fachat/MicroPET/Board/micropet_v2-brd.png

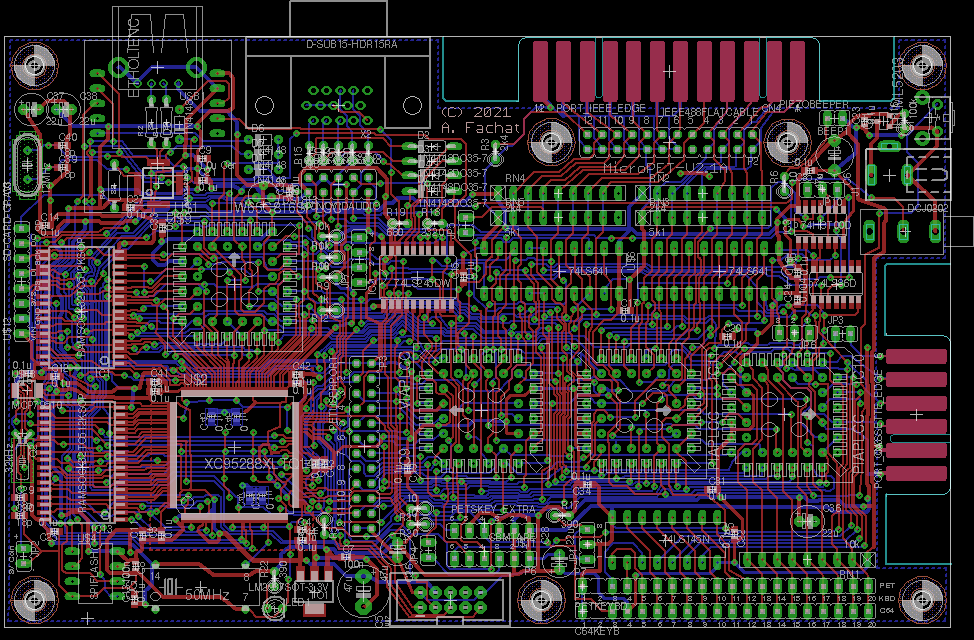
Board/micropet_v2-brd.png
