fachat/MicroPET/Board/micropet_v2-layout.png

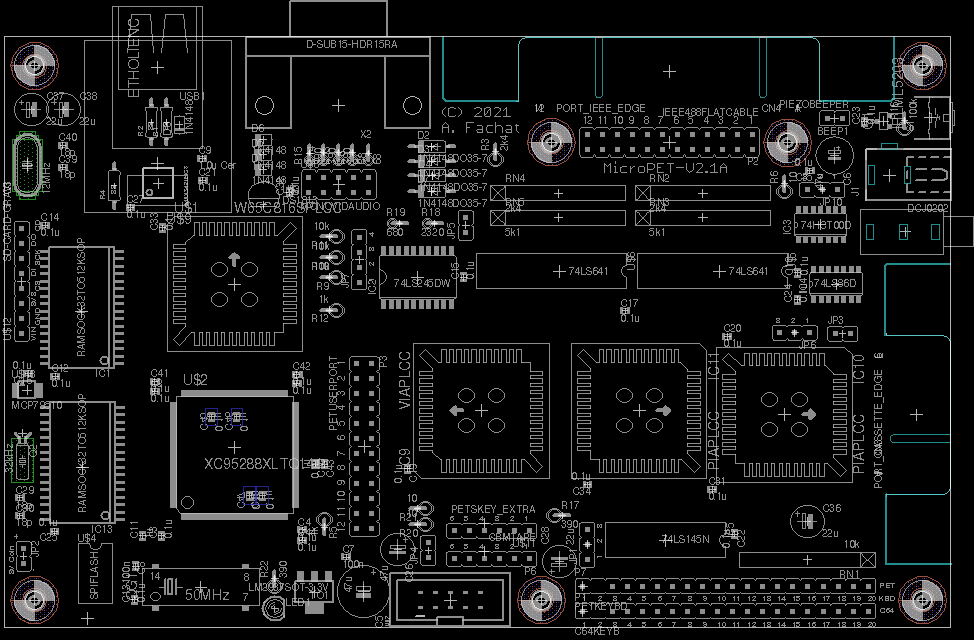
Board/micropet_v2-layout.png
