fachat/MicroPET/Board/micropet_v2-sch-1.png

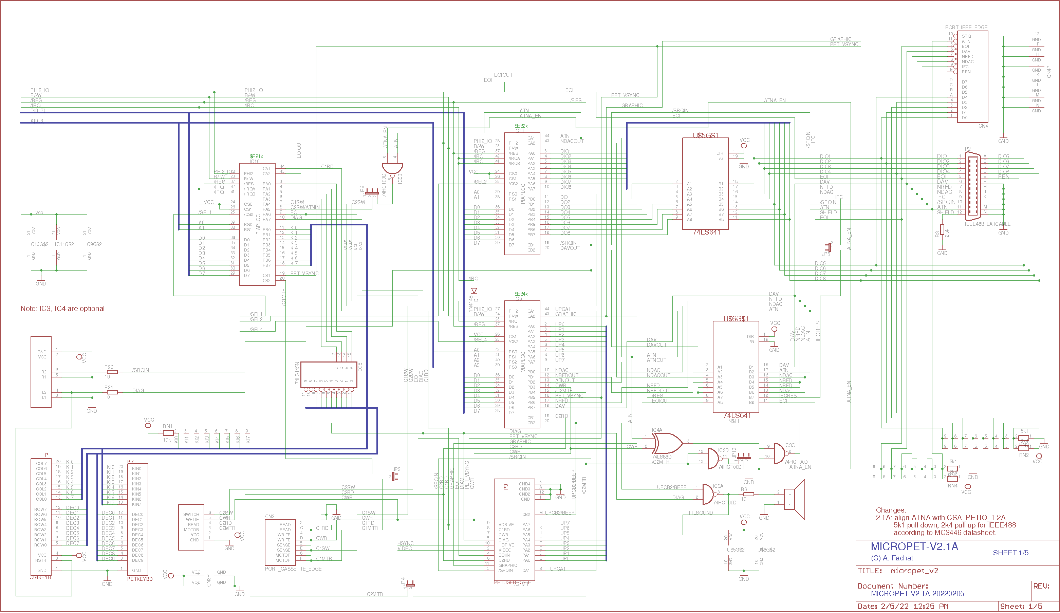
Board/micropet_v2-sch-1.png
