fachat/MicroPET/Board/micropet_v2-sch-2.png

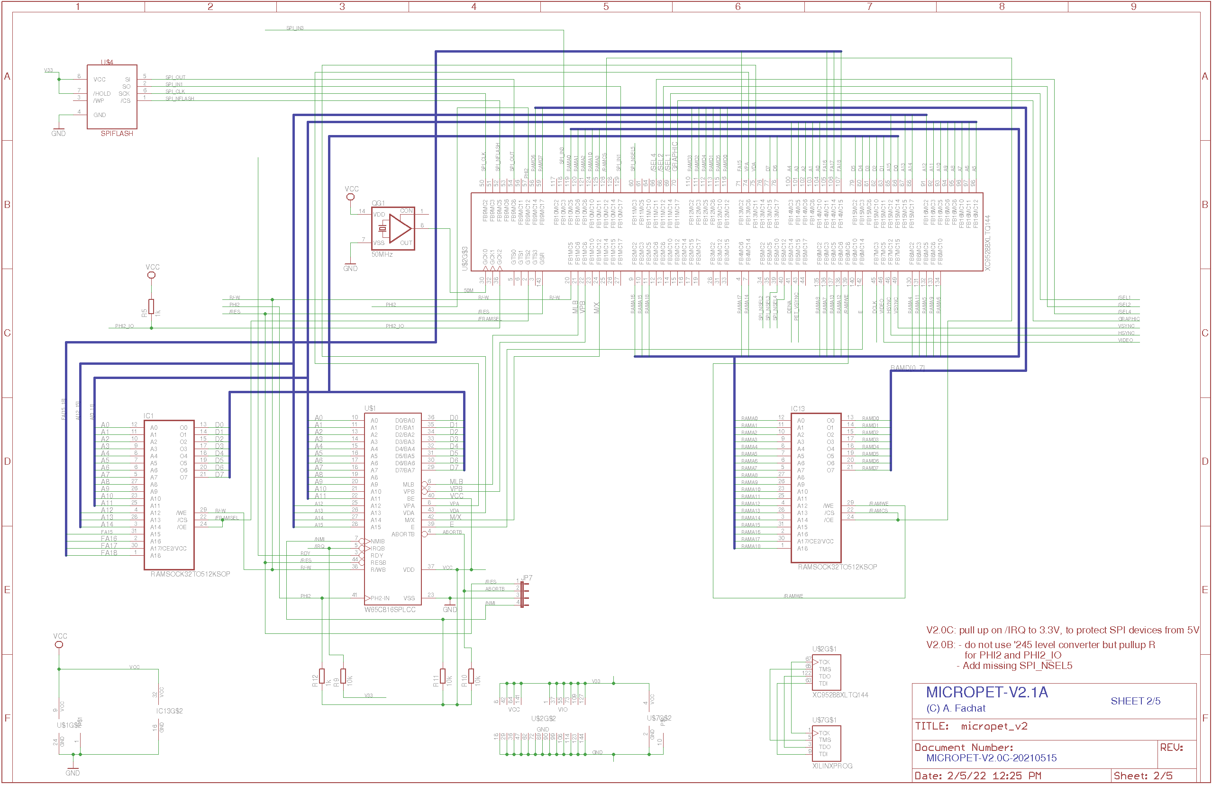
Board/micropet_v2-sch-2.png
