fachat/MicroPET/Board/micropet_v2-sch-3.png

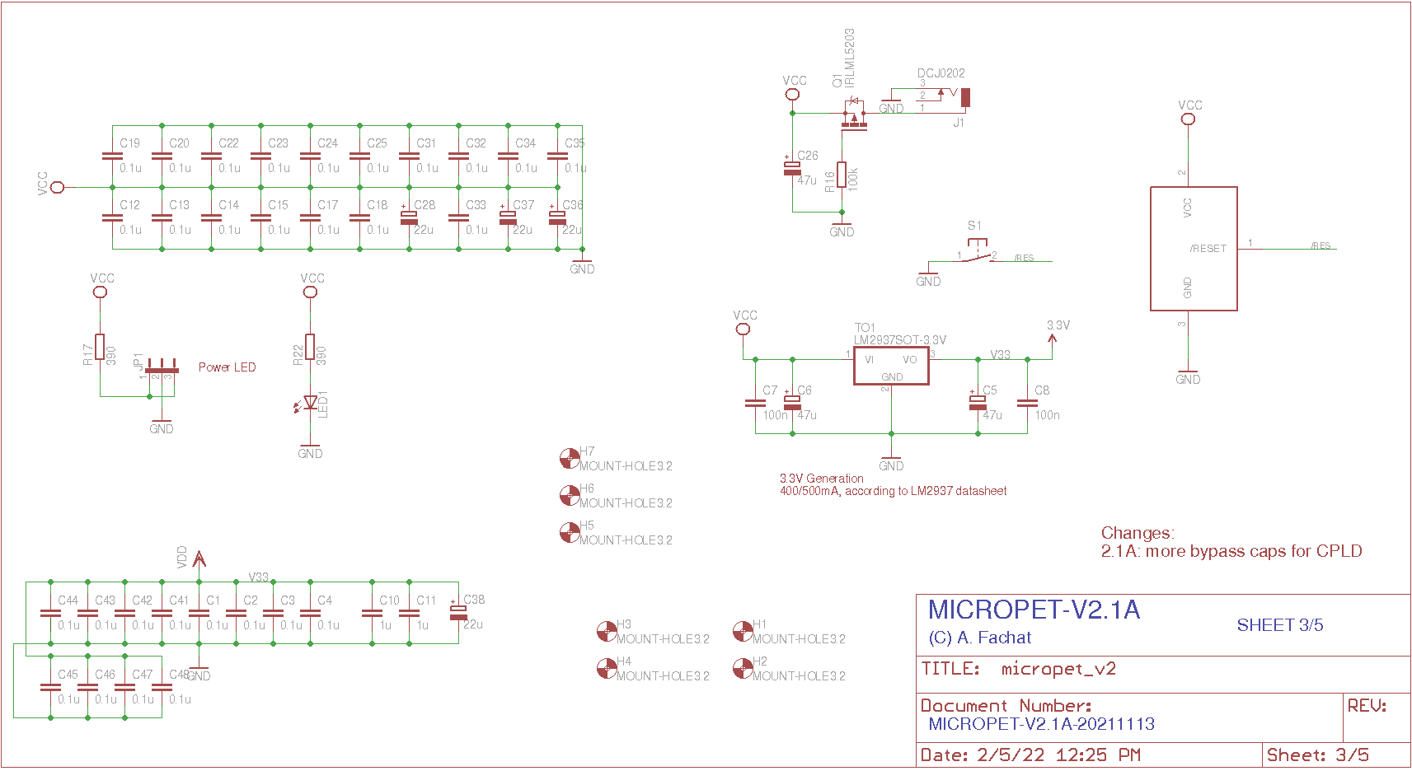
Board/micropet_v2-sch-3.png
