fachat/MicroPET/Board/micropet_v2-sch-4.png

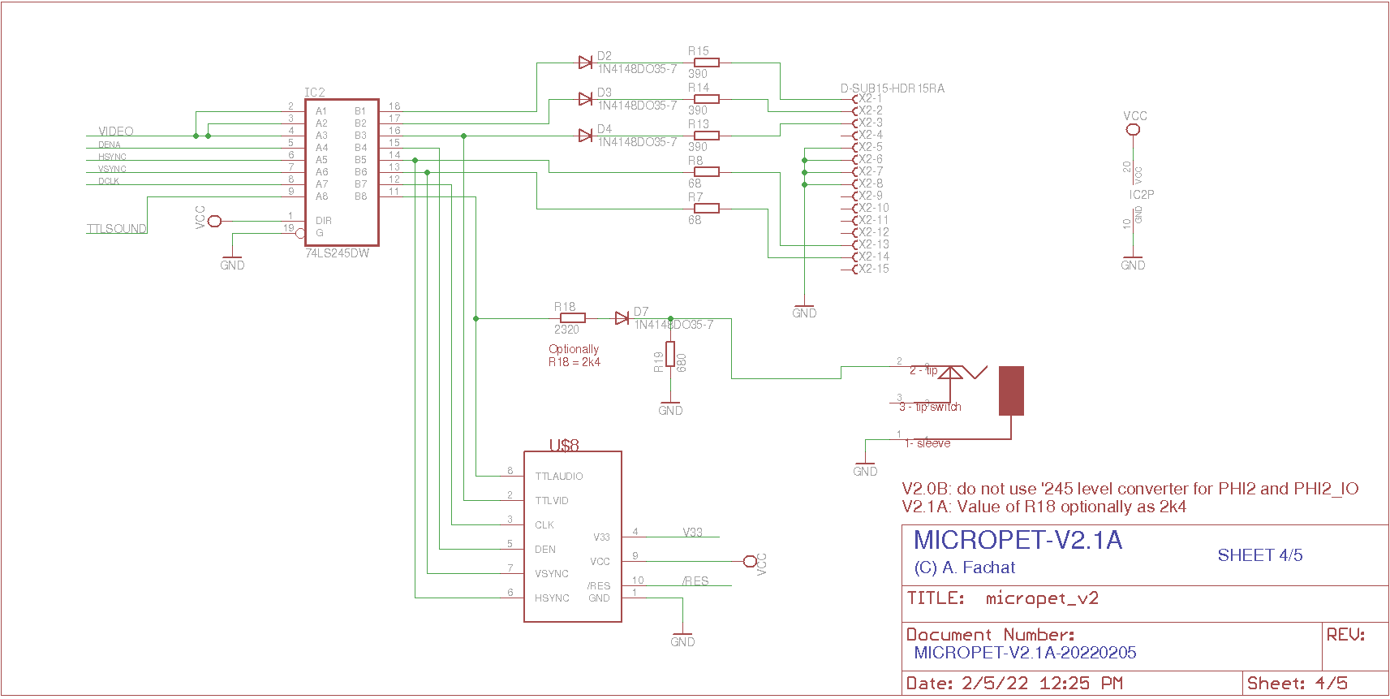
Board/micropet_v2-sch-4.png
