fachat/MicroPET/Board/micropet_v2-sch-5.png

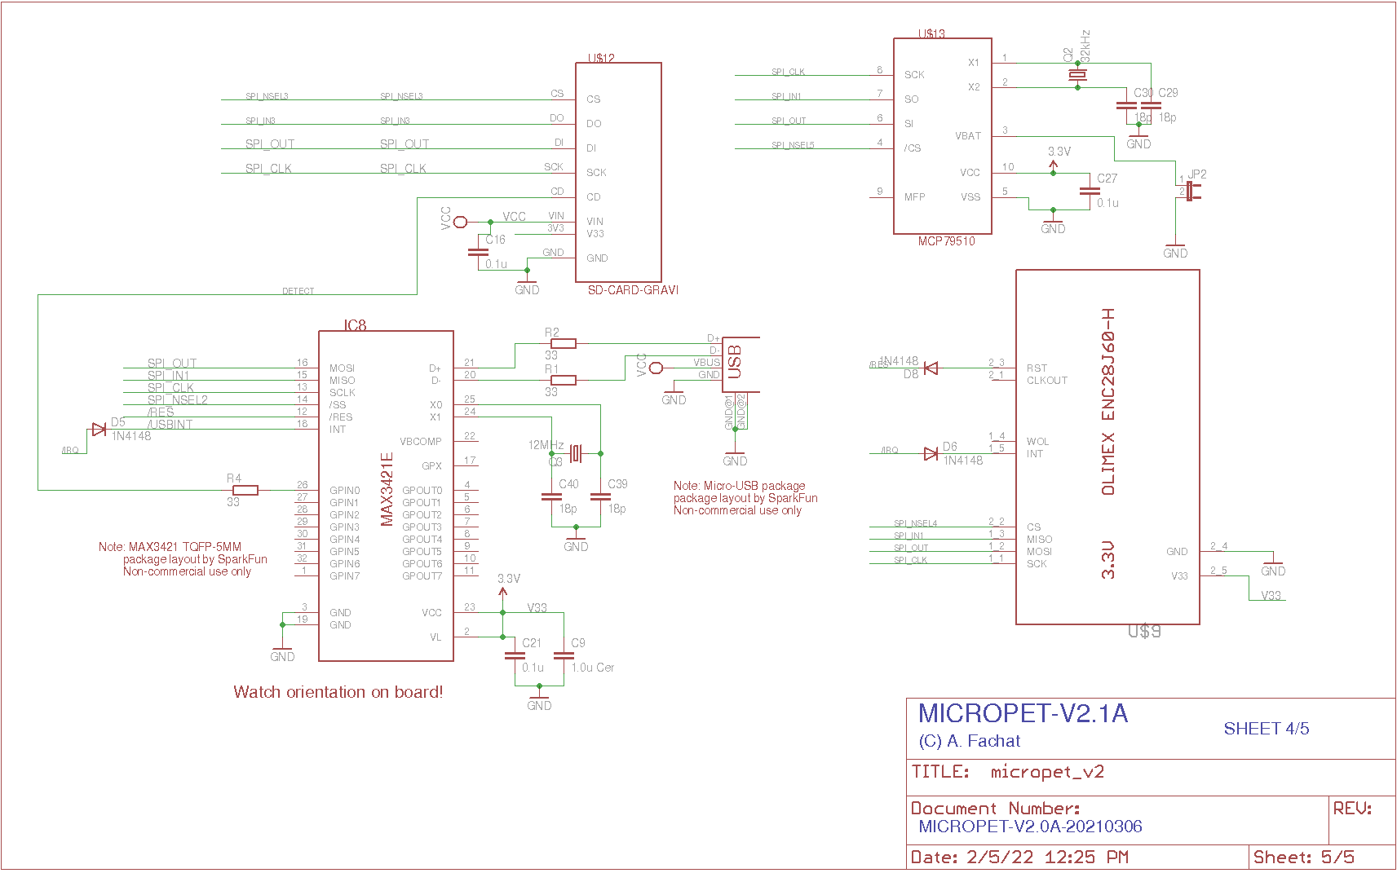
Board/micropet_v2-sch-5.png
